impatrq/SICAP/Pagina Web/README.md

# 🌐 Página Web – Proyecto SICAP

La **página web** del proyecto **SICAP** fue desarrollada como un espacio de difusión, presentación y documentación pública del trabajo realizado por el equipo.  
Su finalidad es mostrar de forma clara y visual el propósito del sistema, su funcionamiento, los integrantes del grupo y el proceso de desarrollo completo.

---

## 🎯 Objetivo

- Dar a conocer el proyecto SICAP a través de una presentación moderna y accesible.  
- Mostrar la **estructura general del sistema**, sus funcionalidades y aplicaciones reales.  
- Centralizar información relevante: descripción del producto, imágenes, agradecimientos y enlaces a redes o repositorios.  
- Facilitar que docentes, evaluadores o interesados puedan entender rápidamente la propuesta del equipo.

---

## 🧩 Descripción general

La página está construida con **HTML, CSS y JavaScript puro**, asegurando compatibilidad con cualquier navegador sin necesidad de frameworks externos.  
Se compone de distintas secciones que resumen las partes más importantes del proyecto:

- **Inicio:** Presentación visual del sistema y resumen del propósito general.  
- **Funcionamiento:** Explicación técnica básica del sistema RFID y sus módulos (firmware, hardware y servidor).  
- **Equipo de trabajo:** Breve perfil de los integrantes con enlaces a sus redes profesionales.  
- **Agradecimientos:** Reconocimiento a docentes, institución y personas que acompañaron el desarrollo.  
- **Multimedia:** Imágenes del sistema en funcionamiento, esquemas y fotos del prototipo final.

---

## 💻 Tecnologías utilizadas

- **HTML5** – Estructura y contenido del sitio.  
- **CSS3** – Estilos, diseño responsivo y animaciones básicas.  
- **JavaScript** – Interactividad y efectos dinámicos.  
- **GitHub Pages** – Publicación gratuita y accesible desde cualquier dispositivo.

---
