impatrq/SICAP/docs/carpeta_de_campo/README.md

# 📘 Carpeta de Campo – Proyecto SICAP

La **carpeta de campo** documenta el proceso completo de desarrollo del proyecto **SICAP**, registrando día a día las actividades, pruebas, avances y correcciones realizadas por el equipo.  
Su objetivo es reflejar de manera cronológica y verificable el trabajo técnico, organizativo y experimental llevado a cabo a lo largo del ciclo 2025.

---

## 🧠 Propósito

- Registrar el avance real del proyecto semana a semana.  
- Dejar evidencia de las tareas individuales y grupales.  
- Documentar los problemas técnicos y las soluciones aplicadas.  
- Servir como respaldo ante evaluaciones y ferias técnicas.  
- Facilitar la trazabilidad del proyecto desde su idea hasta la implementación final.

---

## 📅 Cronología del desarrollo

Cada archivo incluido corresponde a un período específico del desarrollo, detallando los avances logrados y los inconvenientes resueltos en cada etapa.

---

## 🧩 Contenido de los registros

Cada documento mensual incluye:
- Fechas y descripción de las jornadas.  
- Actividades individuales y grupales.  
- Resultados obtenidos y dificultades encontradas.  
- Fotografías o capturas relevantes.  
- Conclusiones parciales y próximos pasos.

---
