impatrq/SICAP/docs/carpeta_de_campo/Junio.md

<h2>Miercoles 28/5/2025</h2>
Lautaro Santolucito:
Durante las 4 horas de profesionalizante de la mañana, Lautaro se encargó del desarrollo de la página web. Específicamente, se dedicó a completar la página, asegurándose de incluir toda la información necesaria y relevante sobre el proyecto y los temas que se abordan en él.

---

Tiziano Patella:
En las 4 horas de profesionalizante de la mañana, Tiziano también estuvo trabajando en el desarrollo de la página web. Su tarea principal fue la resolución de problemas técnicos relacionados con el código. Logró solucionar el inconveniente que afectaba al encabezado (header) y, además, consiguió implementar y hacer funcionales las ventanas modales, en las cuales se detalla la información de cada uno de los integrantes del equipo.

<h2>Jueves 29/05/2025 </h2>

Tiziano Patella:
Durante las 4 horas de la clase de Representación Visual y Frontal de Datos con el profesor Carlassara, Tiziano se dedicó a perfeccionar las ventanas modales de la página. Utilizando la técnica de flex-box, trabajó en el diseño de un espacio que permite que toda la información de los integrantes se visualice correctamente dentro del modal. Adicionalmente, implementó animaciones para mejorar la estética y la experiencia de usuario de la página. Finalmente, integró los enlaces a las cuentas de Instagram y GitHub, facilitando el acceso a las redes sociales de SICAP.

<h2>Martes 4/06/2025</h2>

Lautaro Santolucito: Durante las 4 horas de profesionalizante en el hangar de AVC, Lautaro dedicó 2 horas a la perforación de la placa y, posteriormente, otras 2 horas a la soldadura de los componentes, asegurándose de su correcta fijación.

---

Tiziano Patella: Durante las 4 horas de profesionalizante en el hangar de AVC, Tiziano dedicó 2 horas a la perforación de la placa en conjunto con su compañero, y las 2 horas restantes las empleó en la creación y edición de un video destinado a la publicación en redes sociales, mostrando los avances del proyecto.

<h2>Miercoles 11/06/2025</h2>
Tiziano Patella: Durante las 4hrs de profesionalizante de la mañana se encargo de ajustar los últimos detalles de la pagina web y se finalizar la versión 1.0 de la pagina web. 

---

Lautaro Santolucito: Durante las 4hrs de profesionalizante de la mañana se encargo de rehacer la placa TTL que habían realizando anteriormente los facus y pablo debido a un problema de diseño que surgió y requirió hacer la placa devuelta.

<h2>Jueves 12/06/2025</h2>

Tiziano Patella: Durante las horas de la mañana, me ajustar de arreglar un  problema que había con la pagina web y el header. El problema era que al cambiar el tamaño de la pantalla al de un celular/tablet la pagina se empezaba a ver mal ( en especial el header, en el cual se encimaban todos los links que tenía dificultando la lectura de los mensajes). Tras pedirle ayuda a Medina, el me dijo que la manera de solucionarlo era usando media-query la cual es una función para adaptar paginas a otros dispositivos. Tras muchos intentos, se logro mejorar la forma en la que se veía el header, sin embargo todavía había otros problemas que seguían causando el header no se vea bien. 

<h2>Viernes 13/06/2025</h2>

Tiziano Patella: Durante las 4hrs de profesionalizante de la tarde (con Arguello Padre) se encargo se conseguir un dominio para la pagina web. Se presentaron demasiadas complicaciones ya que una vez comprado el dominio en Hostinger no pedían pagar una mensualidad para el hosting de la pagina web. Ante esa problemática, rembolsamos el dominio comprado ya que creímos que no nos iba a ser útil. Sin embargo tras consultar con compañeros  de otros grupos y con profesores, encontramos la manera de usar el dominio comprado y poder publicar la pagina sin la necesidad de pagar por hosting.  Descubrí que a través de Github pages que puede publicar la pagina guardada en el repositorio de la escuela usando github para el hosting. Así que tras comprar el dominio de vuelta (sicap.site) trabajé junto a fabri para poder configurar todo para la correcta publicación del sitio. Debido al retraso que nos generaron los problemas anteriores lo único que quedó pendiente fue cambiar la url de github pages por las del dominio comprado para que la pagina se muestre  donde nosotros queríamos. 

---

Facu S:

Inicié la **búsqueda de proveedores gráficos** para el diseño y producción de **stickers personalizados del sistema S.IC.A.P**. El objetivo es etiquetar visualmente las herramientas y elementos del sistema con un diseño propio, que incluya el nombre del proyecto y un espacio para la identificación RFID correspondiente.

<h2>Miercoles 18/06/2025</h2>

Facu L:

Me estuve basando en mis conocimientos de diseño electrónico y comunicación de datos, realicé un conjunto de publicaciones centradas en una **placa conversora de señal RS232 a TTL**. Este contenido fue creado con el objetivo de difundir de forma clara y visual el funcionamiento, las características y el propósito de esta placa dentro de un sistema electrónico.
<a href="https://www.instagram.com/p/DLDcrjmur0s/?img_index=1">Publicaion instagram</a>

---

Facu S: 

En primer lugar, realicé pruebas específicas sobre el funcionamiento del conversor **RS232 a TTL**, con el objetivo de asegurar su correcto desempeño antes de integrarlo definitivamente en el sistema. Mediante conexiones controladas y test de comunicación UART, validé que el módulo funcionara de forma estable y sin pérdidas de datos, requisito clave para garantizar la transmisión entre el lector RFID UHF y el ESP32.

Paralelamente, avancé en el estudio y práctica de programación en **MicroPython**, específicamente en la definición de clases que me permitirán estructurar el código del lector RFID de manera más modular y escalable. Esta etapa de aprendizaje fue esencial para preparar el entorno de desarrollo y sentar una base más sólida para los futuros módulos de lectura e identificación.

<h2>Jueves 19/06/2025</h2>

Facu L:

Elabore en canva la publicacion/historia sobre que ya contamos con la pagina web.

<h2>Viernes 20/06/2025 </h2>

Facu S:

Durante la jornada de hoy avancé con la etapa de integración del sistema de lectura RFID, específicamente enfocándome en establecer la comunicación entre el lector UHF y el microcontrolador ESP32 a través del conversor.

Primero, realicé la conexión física del conversor RS232 al ESP32, utilizando los pines adecuados para la interfaz UART. Este conversor me permitió vincular el lector RFID, que opera con protocolo RS232, con mi computadora y posteriormente con el microcontrolador.

Una vez establecida la conexión, desarrollé y cargué un script básico en Python para el ESP32 que permite leer datos entrantes a través del puerto UART. El objetivo era verificar si el sistema lograba detectar etiquetas RFID al aproximarlas al lector.

El código logró el objetivo a medias, ya que se mostraban, pero te tomaba datos mal y no funcionaba del todo bien.

<h2>Lunes 23/06/2025 </h2>

Facu S: 

Durante hoy, me puse como meta poder arreglar el código y hacerle unas modificaciones estéticas y funcionales que me recomendó Carlassara.

Luego de poner a analizar el código, supe lo que corregir, esto eran unas definiciones que tenía que ajustar de la clase que cree para el Reader y así poder tener los datos que precisaba.

El código implementado logró su propósito: pude visualizar en la consola los datos de los tags detectados en tiempo real. Cada vez que una etiqueta RFID era leída por la antena, el ESP32 recibía la señal correctamente y la imprimía por consola, confirmando que la comunicación UART y el flujo de datos eran estables.

Este avance representa un paso importante en la arquitectura del sistema, ya que valida el canal de comunicación entre el lector UHF y el microcontrolador, habilitando así el desarrollo posterior del módulo de identificación y registro de herramientas/personas.

<h2>Miercoles 25/06/2025 </h2>

Facu S:

En el día de hoy trabajé en la mejora del código fuente del sistema **S.IC.A.P**.

El script original presentaba limitaciones tanto en la forma en que se mostraban los datos como en el manejo de lecturas repetidas. Para resolverlo, implementé dos mejoras clave:

- **Formateo de salida en consola**: los tags leídos por el lector RFID se imprimían en una misma línea continua, dificultando el seguimiento en tiempo real. Incorporé **saltos de línea** automáticos para que cada detección aparezca en una nueva línea, mejorando la legibilidad del registro.
- **Sistema de cooldown temporal**: para evitar lecturas redundantes, desarrollé un mecanismo que impide que una misma etiqueta se registre múltiples veces en intervalos muy breves. Este sistema utiliza una ventana de tiempo que bloquea temporalmente la relectura de un mismo tag, asegurando una detección más precisa y ordenada.

Una vez finalizadas las modificaciones, procedimos a **realizar diversas pruebas funcionales** directamente en el sistema. Se colocaron y retiraron múltiples etiquetas RFID en distintos intervalos y posiciones, validando que:

- Cada tag sea leído solo una vez dentro del tiempo establecido.
- El sistema responda en tiempo real con estabilidad.
- La visualización en consola sea clara y segmentada.

Estas pruebas permitieron confirmar el correcto funcionamiento del nuevo código en condiciones reales, consolidando así un avance importante en la fiabilidad y usabilidad del sistema.

<h2>Viernes 27/06/2025 </h2>

<br>
Lautaro Santolucito:<br><br>
Por la tarde, en el horario de Profesionalizantes con el profesor Arguello, decidimos avanzar de forma individual en tareas específicas y que cada uno complete por su cuenta la carpeta de campo en relación con GitHub.

En mi caso, resolví algunos problemas que tenía con GitHub Desktop y me enfoqué a fondo en organizar, subir y acomodar correctamente los archivos del proyecto en el repositorio. Me aseguré de que todo quede bien claro, ordenado y completo. Quedé conforme con el resultado final.

Además, en la última hora de clase aproveché para investigar sobre los servidores que vamos a necesitar para gestionar la información cuando se lean las etiquetas RFID, y sobre cómo montar una página interactiva hosteada directamente por ese servidor.

---

Facu L:

Elabore las imagenes para poder usar en la pagina web y que quede mucho mas estetico. 

---

Facu S:

El trabajo del día de ayer consistió en el refinamiento del código principal del lector RFID. Específicamente, hice una mejora del módulo de cooldown ya implementado, corrigiendo errores preexistentes para asegurar su correcto funcionamiento y optimizar su comportamiento. Esta tarea fue clave para prevenir lecturas redundantes de manera más eficaz. También continué mejorando la salida de datos por consola, consolidando el sistema que agrupa las lecturas de un mismo tag y muestra un contador (ej: A232456 X3), lo cual simplifica significativamente el monitoreo durante las pruebas. Finalmente, se dediqué tiempo a tareas de gestión, actualizando tanto la documentación personal en la carpeta de campo como el estado de las tareas en el tablero de Trello.

---

Patella Tiziano:

El día de hoy me encargue de trabajar en unos problemas que se estaban generando en la pagina web.La problemática que generaban los modales a la pagina era que al pasar por su respectiva seccion estos causaban bajones en las personas que querian ver la pagina y altos tiempo de carga, ante esta problematica busque una forma de solucionar el trabado que generaban el mal funcionamiento de la pagina. Tras hablar con el profe Medina el me recomendó que el problema podría estar en las imágenes y no en el modal como tal, por lo  que tras reducir el peso de la imágenes y ajustar otros valores para que queden mejor las nuevas imágenes se logro solucionar la problemática de los modales.

<h2>Lunes 30/06/2025</h2>

Lautaro Santolucito: 

Durante la jornada de hoy estuve trabajando en la configuración inicial del servidor con Django, que va a ser el encargado de recibir los datos del ESP32 dentro del sistema S.I.C.A.P. Arranqué creando el proyecto desde cero, generé la app para manejar los registros RFID y definí el modelo de base de datos para guardar los tags.

Después programé un endpoint que permite recibir datos por POST en formato JSON, y estuve haciendo pruebas locales con curl para confirmar que los datos llegaran bien y se guardaran correctamente. También configuré el servidor para que se pueda acceder desde otros dispositivos de la red, agregando mi IP a ALLOWED_HOSTS y levantando el servidor en modo público dentro de la red local.

Por ahora estoy en fase de pruebas. Todavía no empecé a probar con el ESP32 porque antes quiero dejar el servidor bien afilado, estable y funcionando sin errores. La integración con el microcontrolador va a ser el siguiente paso una vez que esté todo listo del lado del backend

---

Patella Tiziano:

El día de hoy me encargue de hacer unos ajustes al inicio de la pagina web. Tras haber cambiado la imagen de inicio por el collage que hizo Facundo Ledesma, nos dimos cuenta que el nuevo fondo afectaba la legibilidad del titulo y subtitulo del proyecto, asi que tras consultar con mis compañeros por la estetica que ellos preferian termine modificando para presentar un inicio de la pagina adecuado. Una vez finalizada esa tarea ( y dando finalizada la primera version de la pagina web) me encaegue de comezar con el desarrollo de la web-app. Lo primero que tuve que hacer fue investigar como desarrolla una aplicacion, sin embargo este día no vino ninguno de los profesores de profecionalizante por lo que me tuve que guiar de la informacion de internet y esperar a la proxima para corroborar la informacion con los profes. Tras haber investigado terminé encontrando una aplicacion (Bubble) en la cual podiamos hacer la aplicacion sin escribir ninguna linea de codigo, sin embargo no sabia si iba a ser util para lo que necesitamos hacer por lo que preferí no profundizar mas en el tema y esperar para realizar consultas.
