impatrq/SICAP/docs/carpeta_de_campo/Carpeta-de-campo-15_5-27_6.md

# Bitácora Personal – Lautaro Santolucito  
**Proyecto SICAP – Escuela Técnica N.º 7 “Taller Regional Quilmes”**  
**Inicio: 15/05/2025**

---

📅 15/05/2025 – Parte 1  
✅ Tareas realizadas:  
- Me ofrecí a colaborar con el diseño de la placa para avanzar en conjunto.  
- Se acercó el profesor Arguello y nos informó que debíamos reunirnos en la sala del entrepiso a las 14:00 h.  
💬 Propuestas realizadas:  
- Sugerí dividir las tareas del diseño de la placa para que cada integrante colabore de forma ordenada.  
❗ Situación del grupo:  
- Aún no se definió con precisión qué circuito se debe diseñar.  
- No se ha propuesto un esquema de distribución de tareas para el trabajo de la placa.  
- El grupo continúa sin un plan concreto para abordar esta nueva etapa del proyecto.  
- No está definida la manera en que se va a hacer la carpeta de campo del proyecto.  
📊 Próximas acciones posibles:  
- Proponer una división de tareas equitativa: búsqueda del circuito, esquemático en Proteus, diseño de la PCB, presupuesto e informe.  
- Documentar diariamente los aportes individuales para mayor claridad y orden.  
- Proponer finalmente cómo se va a desarrollar la carpeta de campo de manera ordenada y prolija.

📅 15/05/2025 – Parte 2 (después de las 14:00 h)  
✅ Tareas realizadas:  
- Participamos de la clase de Arguello desde las 14:00 h hasta las 17:30 h en el entrepiso.  
- Se trabajó en los trabajos prácticos de su materia.  
- El profesor trajo instrumental donado, que se comenzó a testear para verificar su funcionamiento.

---

📆 Semana del 18 al 24 de mayo  

📅 20/05/2025  
✅ Tareas realizadas:  
- Luego de la clase de Garabato, nos reunimos para avanzar con el diseño del circuito de la plaqueta.  
- Comenzamos a buscar circuitos posibles.  
- Los chicos trabajaron en el presupuesto de materiales.  
- Se realizaron varias consultas con el profesor Fabrizio para confirmar qué componentes se necesitan.  
- Se analizó qué materiales conviene comprar según disponibilidad y presupuesto.  
💬 Propuestas realizadas:  
- Consolidar el diseño de la placa con un circuito viable y empezar la compra de componentes.  
❗ Situación del grupo:  
- Se mantiene una actitud participativa y colaborativa.  
- Aún se está evaluando el circuito definitivo para implementar.

📅 21/05/2025  
✅ Tareas realizadas:  
- Se reorganizó y limpió por completo el espacio de trabajo del grupo.  
- Se consiguió un nuevo locker para guardar herramientas y materiales.  
- Se reacomodaron los escritorios para optimizar el uso del espacio.  
💬 Propuestas realizadas:  
- Dejar asentado un esquema visual del orden del espacio para mantenerlo en el tiempo.  
❗ Situación del grupo:  
- Mejora notable en la organización del entorno de trabajo.  
- Se fortalece el compromiso grupal con el proyecto desde lo logístico.

📅 22/05/2025  
✅ Tareas realizadas:  
- Facundo Ledesma trabajó en Canva preparando diapositivas para la presentación con la inspectora.  
- Pablo leyó documentación sobre los lectores.  
- Facundo Spagnoletta avanzó con el diseño de la plaqueta del conector RS232 a TTL en KiCad.  
- Tiziano exploró avances en el desarrollo de la página web.  
- Lautaro completó la carpeta de campo, colaboró con Ledesma aportando ideas para el Canva y supervisó el trabajo de Spagnoletta.  
💬 Propuestas realizadas:  
- Consolidar los avances individuales en una presentación grupal clara y visual.  
❗ Situación del grupo:  
- Cada integrante asumió una tarea específica y se notó compromiso general.  
- Se trabaja de forma paralela en las distintas áreas del proyecto (documentación, diseño, programación, presentación).

📅 23/05/2025  
✅ Tareas realizadas:  
- Se desarrollaron clases normales durante la mañana.  
- El profesor Sergio Medina no asistió a su hora correspondiente de profesionalizantes.  
- A pesar de la ausencia del profesor, el grupo decidió permanecer en el hangar de aviónica, donde tienen su mesa de trabajo, debido a la visita programada de una inspectora interesada en el proyecto.  
- Se aprovecharon las 4 horas habituales de profesionalizantes para preparar la charla prevista con la inspectora.  
💬 Propuestas realizadas:  
- Permanecer organizados y preparados para exponer el proyecto ante la inspectora.  
❗ Situación del grupo:  
- El grupo muestra compromiso y responsabilidad al mantenerse presente y activo ante situaciones inesperadas.

📅 24/05/2025  
✅ Tareas realizadas:  
- No se registraron actividades del grupo durante el sábado.

---

📆 Semana del 25 al 31 de mayo

📅 26/05/2025  
✅ Tareas realizadas:  
- Se asistió a la escuela pero solo se dictaron 4 horas por la mañana con el profesor Scicolone.  
- Por rotación institucional, se liberó a los alumnos a las 12:00 h.

📅 27/05/2025  
✅ Tareas realizadas:  
- No hubo clases debido a la rotura de un caño de agua perteneciente a la Fuerza Aérea.

📅 28/05/2025  
✅ Tareas realizadas:  
- Lautaro y Tiziano trabajaron las 4 horas de profesionalizantes en la web.  
- Lautaro completó la página con toda la información necesaria sobre el proyecto.  
- Tiziano solucionó problemas del header y logró que las ventanas modales funcionen.

📅 29/05/2025  
✅ Tareas realizadas:  
- Tiziano perfeccionó las ventanas modales usando flexbox y animaciones.  
- Agregó enlaces a Instagram y GitHub.  
- Lautaro colaboró en la estructura y organización del contenido.  
- El resto del grupo realizó horas profesionalizantes en la UTN.

📅 30/05/2025  
✅ Tareas realizadas:  
- El grupo asistió a una exposición en la UADE.

---

📆 Semana del 1 al 7 de junio

📅 02/06/2025  
✅ Tareas realizadas:  
- Se cursó con Scicolone durante 4 horas. Luego, salida por rotación institucional.

📅 03/06/2025  
✅ Tareas realizadas:  
- Lautaro y Tiziano trabajaron en la web.  
- Se completó y ajustó contenido.  
- Se mejoró estructura, animaciones y ventanas modales.

📅 04/06/2025  
✅ Tareas realizadas:  
- Tiziano y Lautaro estuvieron en el hangar mientras los demás iban a la UTN.  
- Se agujereó la placa, se soldaron los componentes, se verificaron pistas.  
- Se hizo y editó un video para publicar en Instagram.

📅 05/06/2025  
✅ Tareas realizadas:  
- Asistencia a charla sobre software libre con Fabrizio.  
- Se valoró su posible aplicación al proyecto.

📅 06/06/2025  
✅ Tareas realizadas:  
- Se verificaron pistas de la placa.  
- Lautaro y Pablo soldaron un microchip.  
- No se alcanzó a probar la placa.

---

📆 Semana del 9 al 14 de junio

📅 09/06/2025  
✅ Tareas realizadas:  
- Se asistió a clase con Solomiewichs y se rindió con Salinas.

📅 10/06/2025  
✅ Tareas realizadas:  
- Lautaro investigó conexiones de la placa y detectó la falta de un pin VCC.  
- Se evaluó rehacer la placa.  
- Tiziano cargó la descripción de los integrantes en la web y se sacaron fotos.  
- Se investigó cómo registrar el dominio del sitio.

📅 11/06/2025  
✅ Tareas realizadas:  
- Lautaro rehízo por completo la placa TTL en su casa y la trajo funcionando.  
- Tiziano dejó lista la versión 1.0 de la web.

📅 12/06/2025  
✅ Tareas realizadas:  
- Tiziano solucionó errores en móviles con media queries.  
- Se discutieron ideas para publicar avances del proyecto en redes.

📅 13/06/2025  
✅ Tareas realizadas:  
- Tiziano y Fabrizio configuraron el dominio `sicap.site` usando GitHub Pages.  
- Se publicó el sitio y se compartió en redes.  
- Se analizó cómo testear la placa con el lector.

---

📆 Semana del 16 al 20 de junio

📅 16/06/2025  
✅ Tareas realizadas:  
- Feriado nacional. No hubo actividades.

📅 17/06/2025  
✅ Tareas realizadas:  
- Se cursó con Montoni.  
- Por la tarde, se probaron conexiones entre la plaqueta TTL y el micro.  
- Se logró comunicación exitosa.

📅 18/06/2025  
✅ Tareas realizadas:  
- Visita a la Universidad Nacional de Quilmes por la mañana.  
- Por la tarde, se conectó exitosamente el microcontrolador al lector RFID.  
- Se detectaron etiquetas correctamente.

📅 19/06/2025  
✅ Tareas realizadas:  
- Jornada reducida por ingreso tardío.  
- Por la tarde se cumplió con tareas de taller sin avanzar en SICAP.

📅 20/06/2025  
✅ Tareas realizadas:  
- Feriado por el Día de la Bandera.

---

📆 Semana del 23 al 28 de junio

📅 23/06/2025  
✅ Tareas realizadas:  
- No se hicieron avances técnicos por tener clase con Salinas.

📅 24/06/2025  
✅ Tareas realizadas:  
- Faltaron la mayoría de los compañeros (día de bioaca).  
- Lautaro no faltó. Investigó a fondo el servidor y la placa.  
- Logró leer etiquetas RFID, mejoró conexiones y fabricó un nuevo cable RS232 hombre–hembra.  
- Por la mañana programó para la materia de Montoni.

📅 25/06/2025  
✅ Tareas realizadas:  
- Se revisó el código para entender por qué no funcionaba y se mejoró.  
- Se lograron leer datos en crudo y el ID de las etiquetas RFID.  
- Se evaluó cómo armar el servidor de almacenamiento.  
- Se corrigió un error en el cable armado.

📅 26/06/2025  
✅ Tareas realizadas:  
- Ingreso tardío institucional.  
- Por la tarde hubo prueba con la profesora Lara.

📅 27/06/2025  
✅ Tareas realizadas:  
- Clases normales a la mañana.  
- Por la tarde, en profesionalizantes, se decidió que cada uno cargue su carpeta en GitHub.  
- Lautaro resolvió problemas con GitHub Desktop, ordenó y subió todos los archivos.  
- Investigó cómo montar un servidor para recibir datos de las etiquetas y hacer una web interactiva.

---

✅ **Fin de bitácora – Última actualización: 28/06/2025**
