impatrq/SICAP/hardware/conversor_rs232_ttl/Segunda_Placa/Impresion.pdf

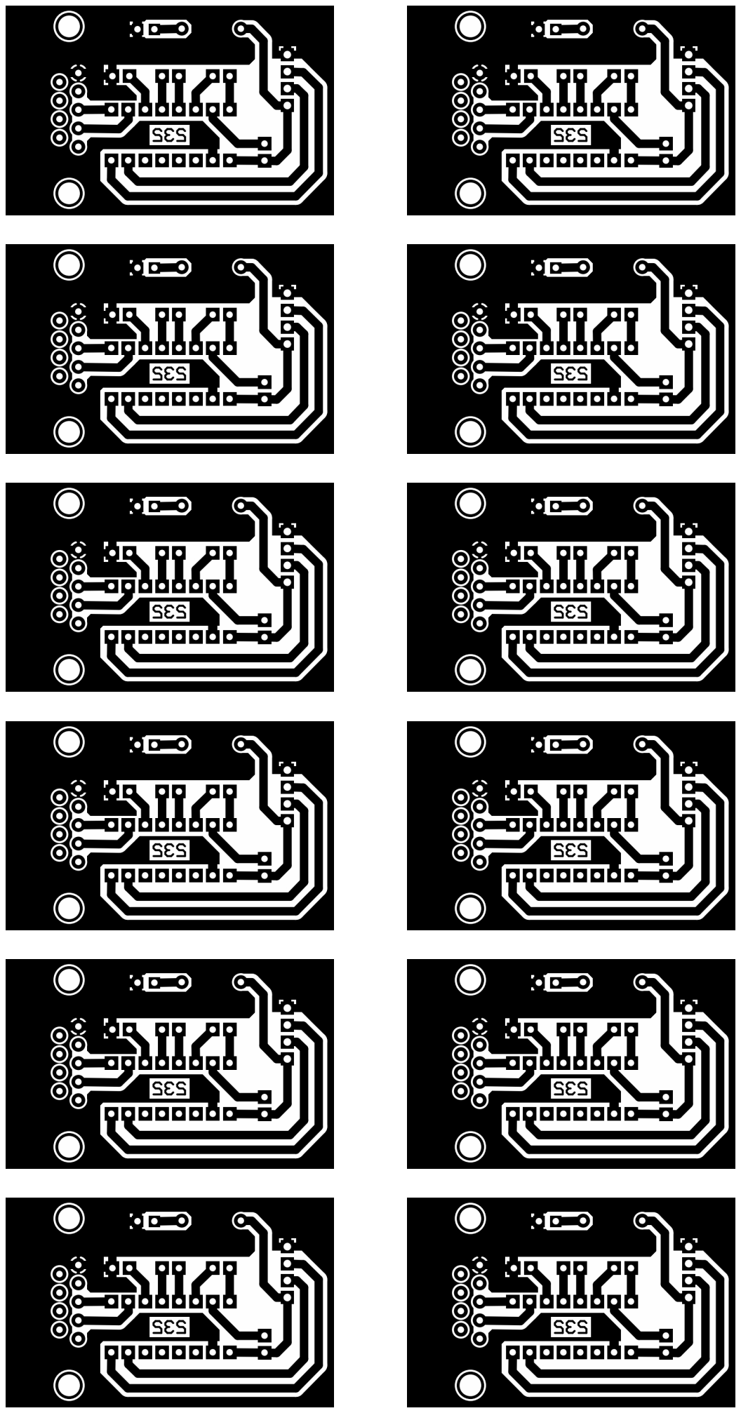
[picture p18: page 1]
