impatrq/SICAP/Pagina Web/images/background 2.png

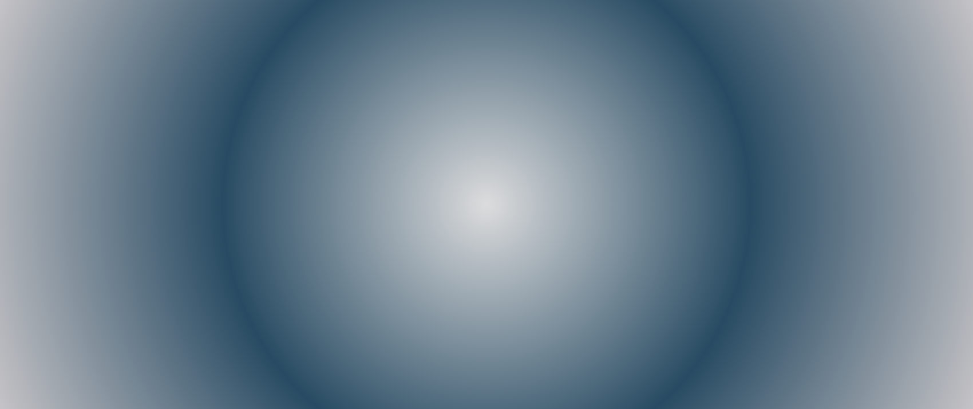
Pagina Web/images/background 2.png
