impatrq/SICAP/Pagina Web/images/Bibliotecario.jpg

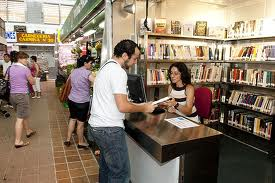
Pagina Web/images/Bibliotecario.jpg
