impatrq/SICAP/Pagina Web/images/Checkpoint.png

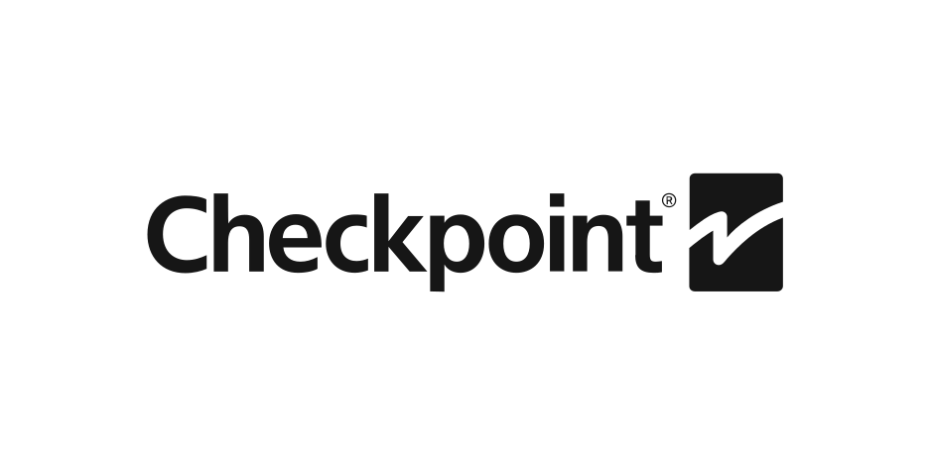
Pagina Web/images/Checkpoint.png
