impatrq/SICAP/Pagina Web/images/facul.jpg

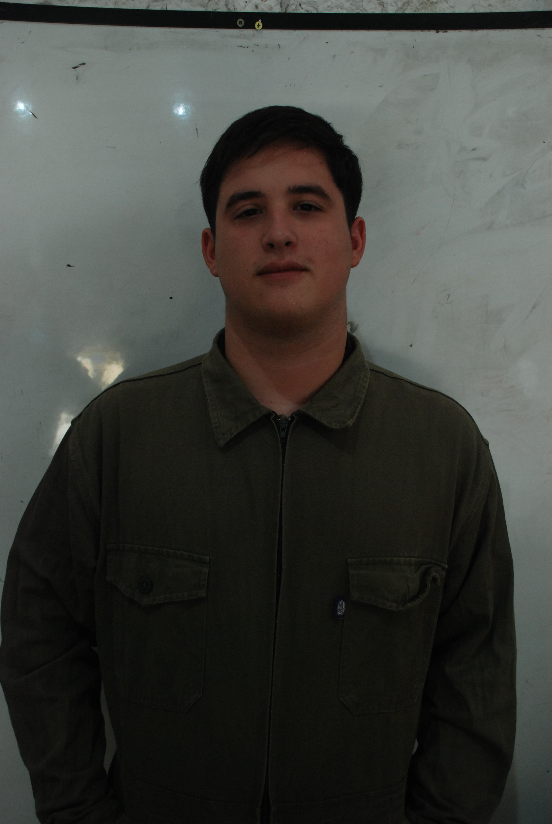
Pagina Web/images/facul.jpg
