impatrq/SICAP/Pagina Web/images/facus.jpg

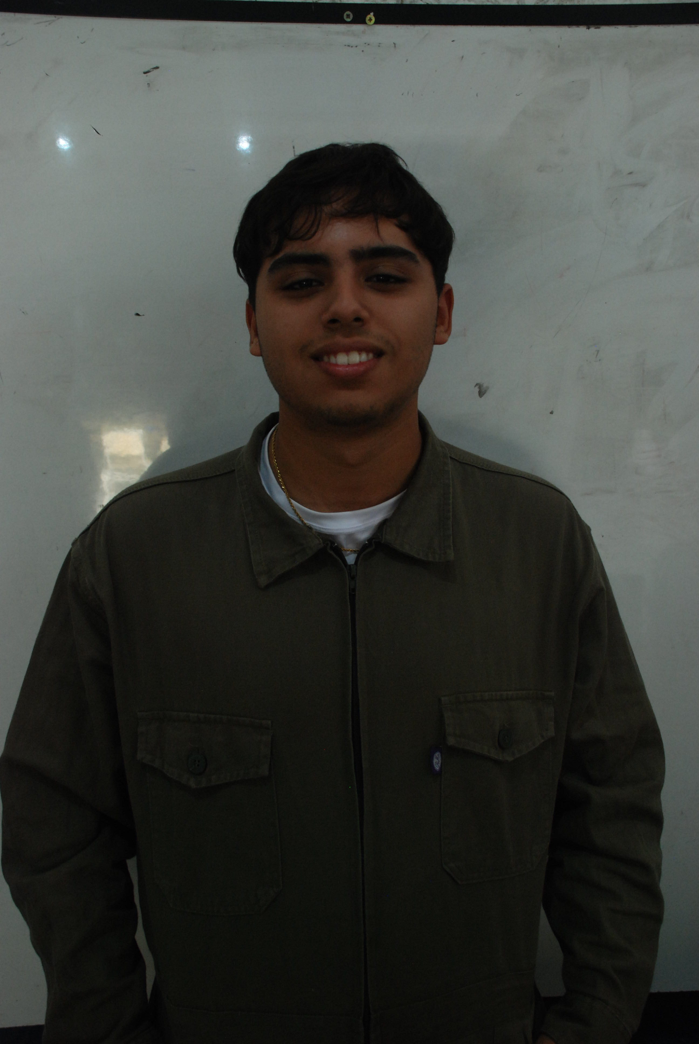
Pagina Web/images/facus.jpg
