impatrq/SICAP/Pagina Web/images/Ledmull.png

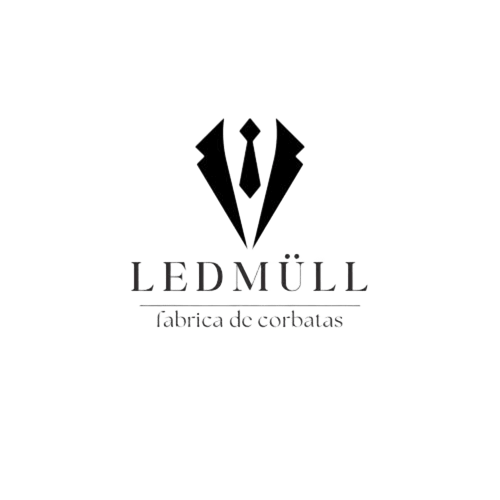
Pagina Web/images/Ledmull.png
