impatrq/SICAP/Pagina Web/images/Miloser.png

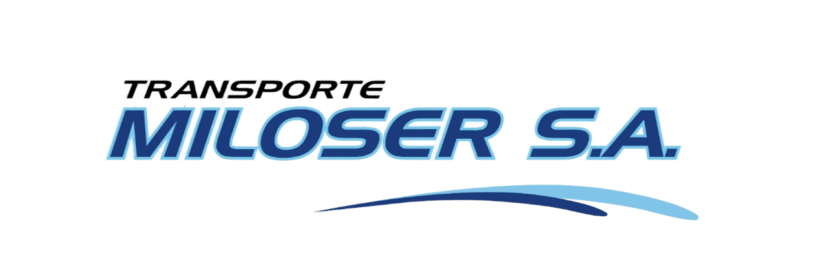
Pagina Web/images/Miloser.png
