impatrq/SICAP/Pagina Web/images/new-pablo.jpg

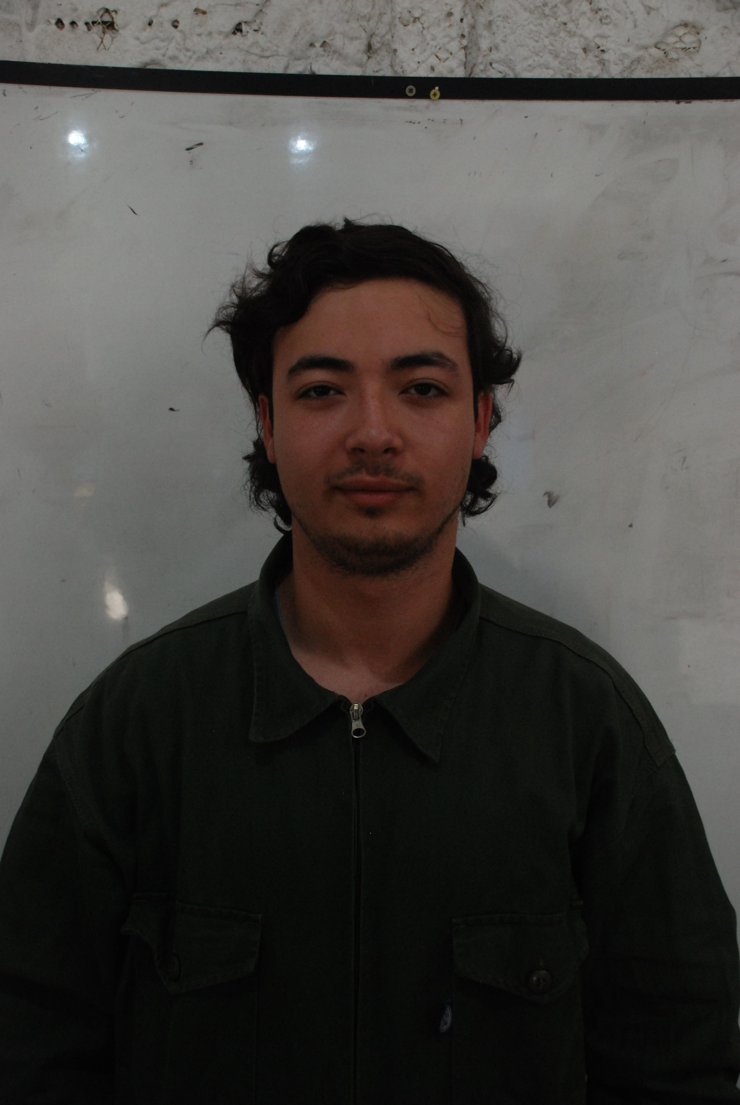
Pagina Web/images/new-pablo.jpg
