impatrq/SICAP/Pagina Web/images/newcollage.jpg

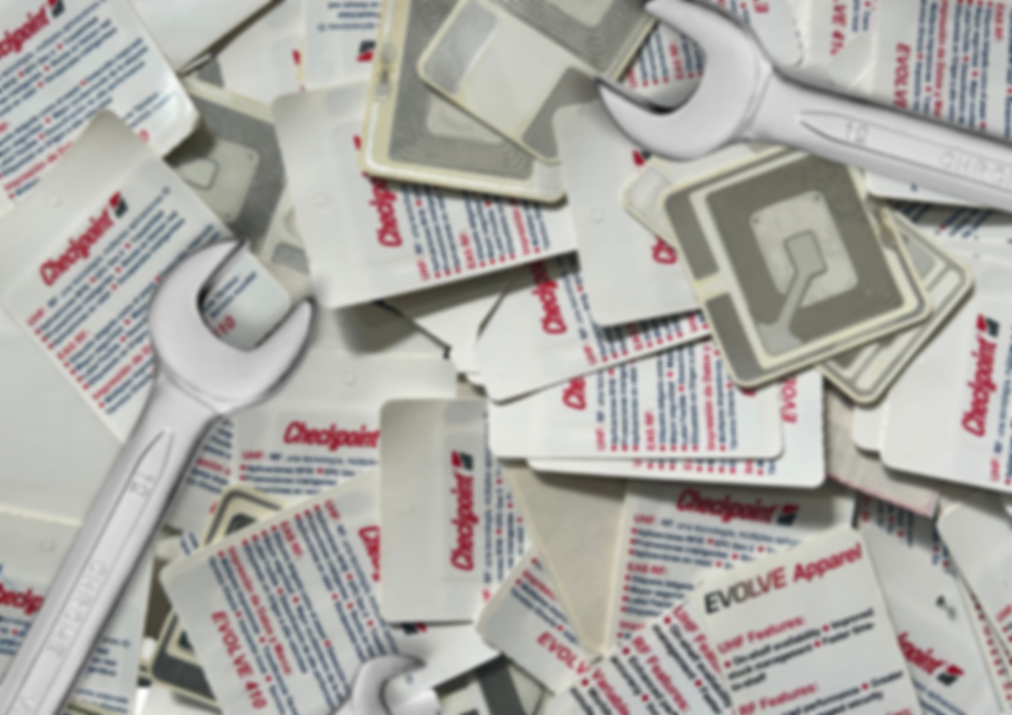
Pagina Web/images/newcollage.jpg
