impatrq/SICAP/Pagina Web/images/pantalla principal 1.png

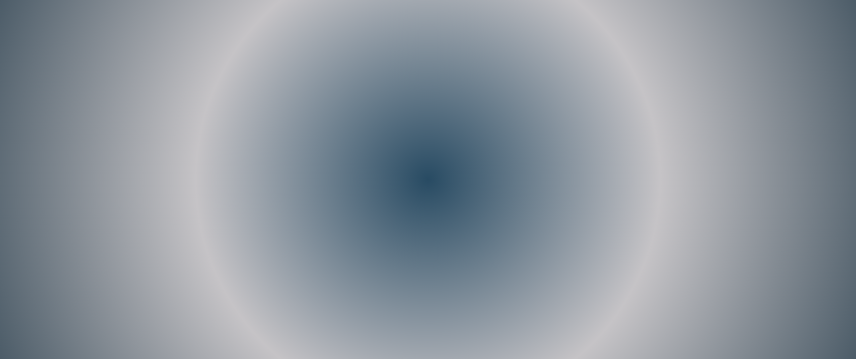
Pagina Web/images/pantalla principal 1.png
