impatrq/SICAP/Pagina Web/images/pantalla principal 2.png

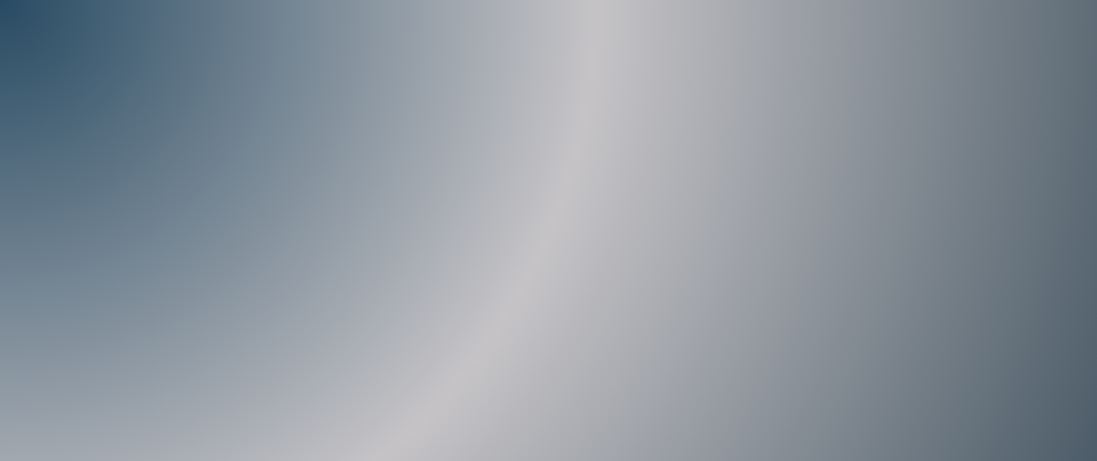
Pagina Web/images/pantalla principal 2.png
