impatrq/SICAP/Pagina Web/images/pañol.jpeg

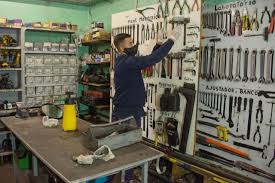
Pagina Web/images/pañol.jpeg
