impatrq/SICAP/Pagina Web/images/supermercado.png

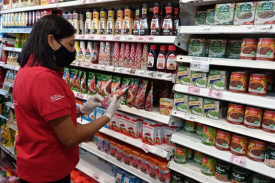
Pagina Web/images/supermercado.png
