impatrq/SICAP/Web-app/web-app/src/assets/Images/Fondo-home.jpg

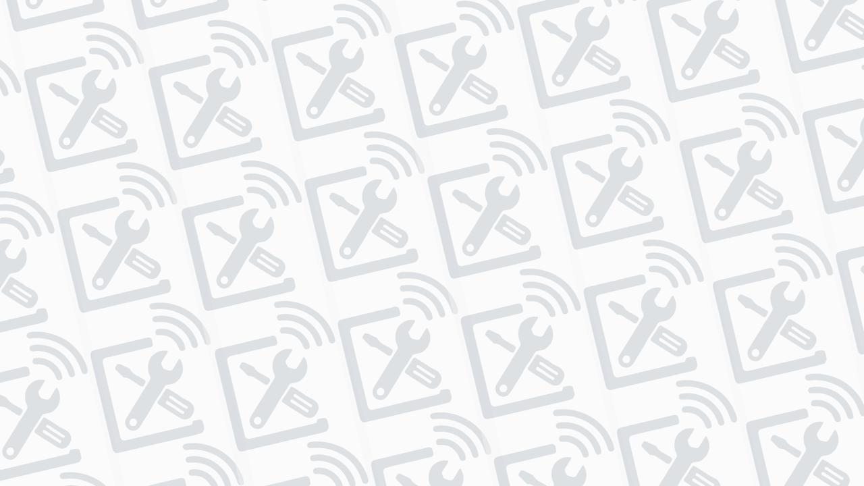
Web-app/web-app/src/assets/Images/Fondo-home.jpg
