impatrq/SICAP/Web-app/web-app/src/assets/Images/Fondo-login.jpg

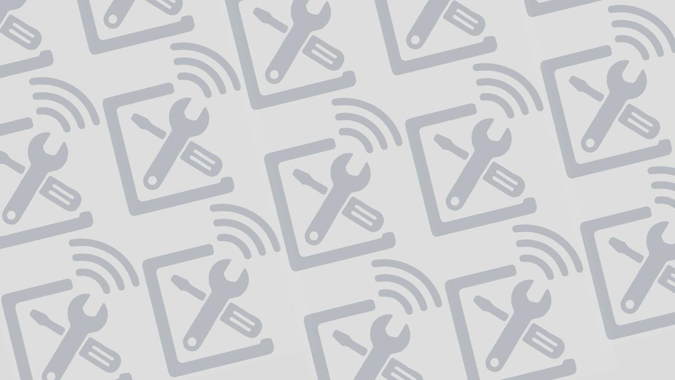
Web-app/web-app/src/assets/Images/Fondo-login.jpg
