impatrq/SICAP/Web-app/web-app/src/assets/Images/Sicap-grande.png

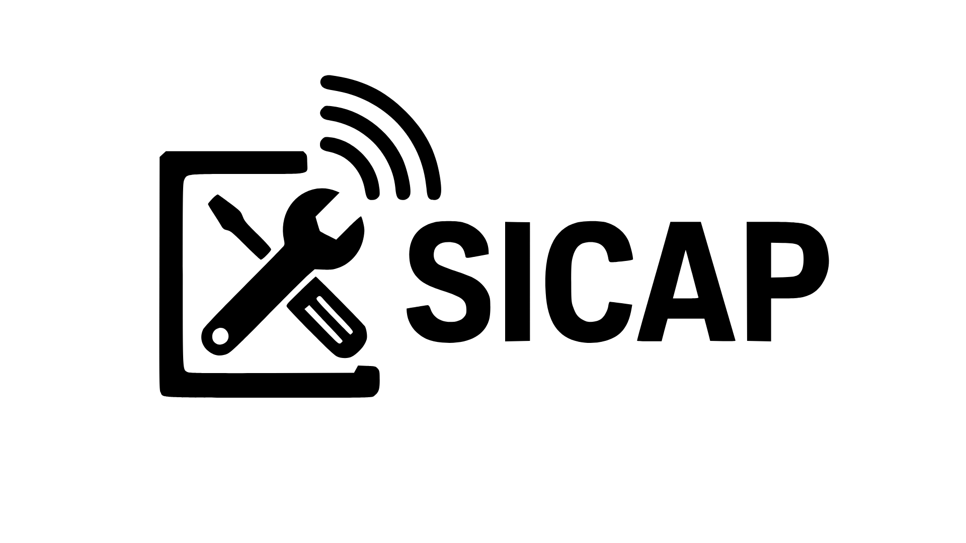
Web-app/web-app/src/assets/Images/Sicap-grande.png
