impatrq/SICAP/Servidor-sicap_backend/SICAP_Backend/registros/serializer.py

"""
Serializadores del módulo `registros`.

Contienen las representaciones API de `Panol`, `RegistroTag` y
`Asignacion` utilizadas por los endpoints REST.
"""

from rest_framework import serializers
from rest_framework.viewsets import ModelViewSet
from rest_framework.permissions import IsAuthenticatedOrReadOnly
from .models import Panol, RegistroTag, Asignacion


class PanolSerializer(serializers.ModelSerializer):
    class Meta:
        model = Panol
        fields = ["id", "nombre", "icono"]


class RegistroTagSerializer(serializers.ModelSerializer):
    categoria = serializers.ChoiceField(
        choices=["persona", "insumo"], allow_null=True, required=False
    )
    created_at = serializers.SerializerMethodField(read_only=True)

    class Meta:
        model = RegistroTag
        fields = ["nombre", "categoria", "id", "tag", "fecha_hora", "created_at"]

    def get_created_at(self, obj):
        from django.utils.timezone import localtime

        return localtime(obj.fecha_hora).strftime("%Y-%m-%d %H:%M:%S")


class AsignacionSerializer(serializers.ModelSerializer):
    class Meta:
        model = Asignacion
        fields = [
            "id",
            "persona_tag",
            "persona_nombre",
            "item_tag",
            "item_nombre",
            "asignado_en",
            "devuelto_en",
            "activo",
        ]
