impatrq/SICAP/Servidor-sicap_backend/SICAP_Backend/usuarios_login/apps.py

"""Configuración de la app `usuarios_login`."""

from django.apps import AppConfig


class UsuariosLoginConfig(AppConfig):
    default_auto_field = "django.db.models.BigAutoField"
    name = "usuarios_login"
