impatrq/SICAP/Pagina Web/images/new-facul.jpg

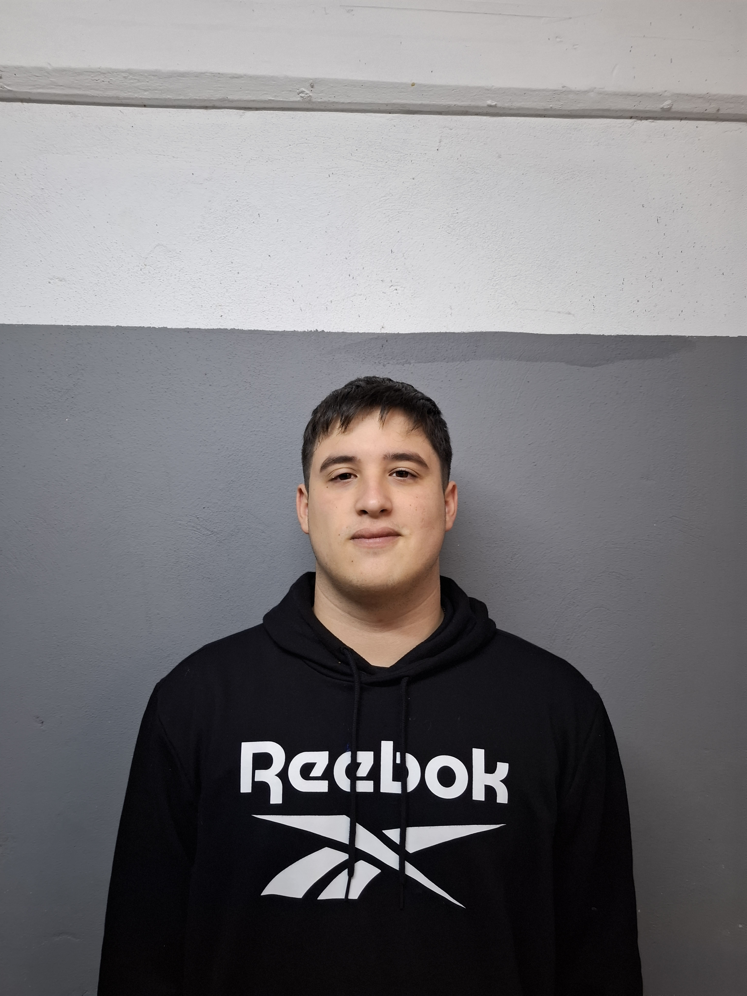
Pagina Web/images/new-facul.jpg
