impatrq/SICAP/Pagina Web/images/new-lauty.jpg

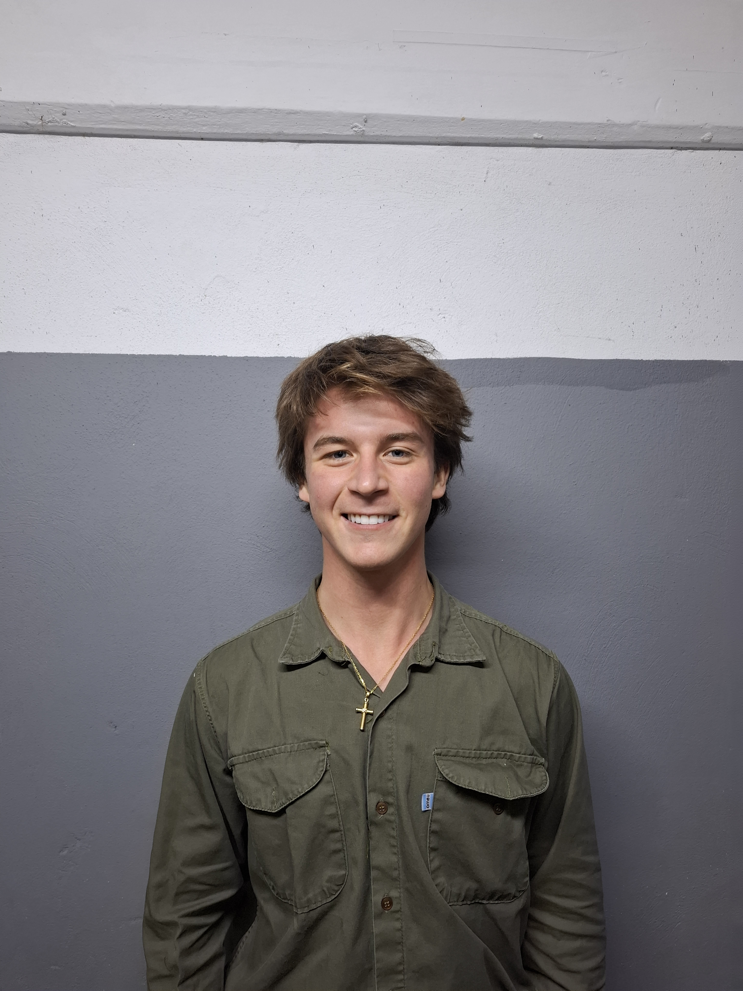
Pagina Web/images/new-lauty.jpg
